RTES-Group/DigitSynth/application/src/voltage-scaler.cpp

#include "voltage-scaler.hpp"

using namespace voltage_scaler;

VoltageScaler::VoltageScaler() {}

float VoltageScaler::scale(float v, ADS1115settings::Input channel) {
    if (v > this->maxes[channel]) { this->maxes[channel] = v; }
    if (v < this->mins[channel])  { this->mins[channel] =  v; }
    
    return (v - this->mins[channel]) / (this->maxes[channel] - this->mins[channel]);
}
